littlebits/o21-number/firmware/LB_BIT_o21_number-v03(rev5_4)/src/pwm_lookup.h

/*
 * pwm_lookup.h
 *
 * Created: 2/13/2014 5:38:29 PM
 *  Author: Rory
 *
 * Copyright 2014 littleBits Electronics
 *
 * This file is part of o21-number.
 *
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
 * o21-number is distributed in the hope that it will be useful,
 * but WITHOUT ANY WARRANTY; without even the implied warranty of
 * MERCHANTABILITY or FITNESS FOR A PARTICULAR PURPOSE.  See the
 * GNU General Public License at <http://www.gnu.org/licenses/> for more details.
 */ 


#ifndef PWM_LOOKUP_H_
#define PWM_LOOKUP_H_

const uint16_t pwm_lookup[100] =
{
	0,		/* 0 */
	12,		/* 1 */
	20,		/* 2 */
	32,		/* 3 */
	40,		/* 4 */
	51,		/* 5 */
	60,		/* 6 */
	72,		/* 7 */
	80,		/* 8 */
	92,		/* 9 */
	101,	/* 10 */
	112,	/* 11 */
	121,	/* 12 */
	133,	/* 13 */
	139,	/* 14 */
	149,	/* 15 */
	160,	/* 16 */
	169,	/* 17 */
	180,	/* 18 */
	189,	/* 19 */
	202,	/* 20 */
	212,	/* 21 */
	225,	/* 22 */
	235,	/* 23 */
	244,	/* 24 */
	258,	/* 25 */
	264,	/* 26 */
	278,	/* 27 */
	284,	/* 28 */
	298,	/* 29 */
	308,	/* 30 */
	320,	/* 31 */
	328,	/* 32 */
	338,	/* 33 */
	344,	/* 34 */
	359,	/* 35 */
	364,	/* 36 */
	379,	/* 37 */
	384,	/* 38 */
	396,	/* 39 */
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
};

#endif /* PWM_LOOKUP_H_ */
